myprotoai/demo/samples/circular/images/05-troubleshooting/53-solder-bridge-identification.png

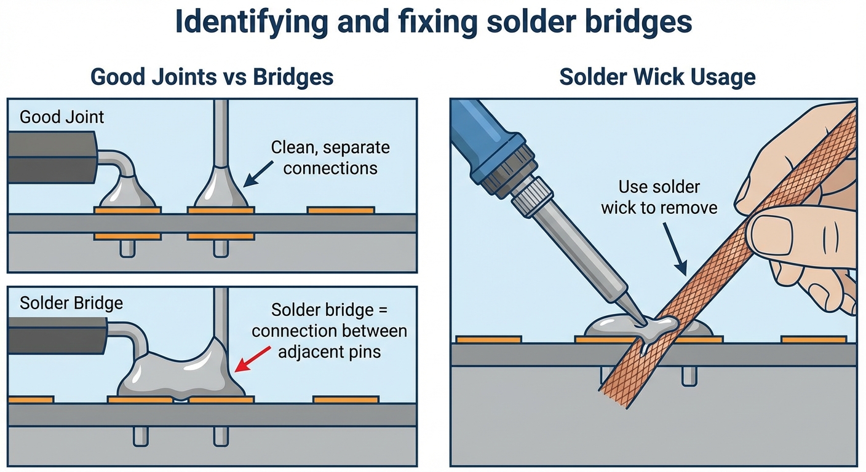
samples/circular/images/05-troubleshooting/53-solder-bridge-identification.png
