myprotoai/demo/samples/circular/images/05-troubleshooting/54-cold-solder-joints.png

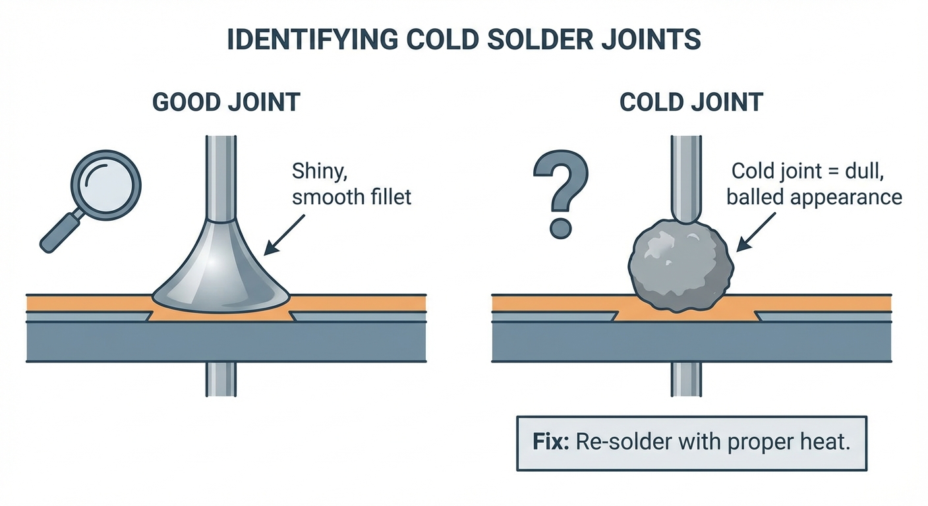
samples/circular/images/05-troubleshooting/54-cold-solder-joints.png
