myprotoai/demo/samples/teardrop/images/05-troubleshooting/53-solder-bridge-identification-teardrop.png

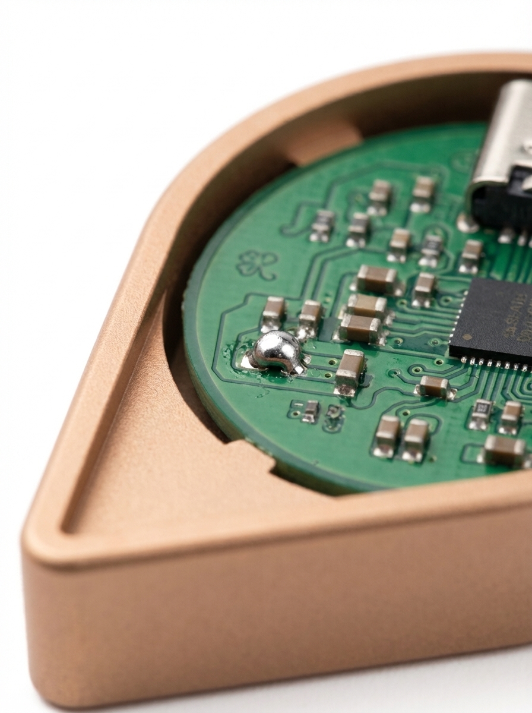
samples/teardrop/images/05-troubleshooting/53-solder-bridge-identification-teardrop.png
