myprotoai/demo/samples/teardrop/images/05-troubleshooting/54-cold-solder-joints-teardrop.png

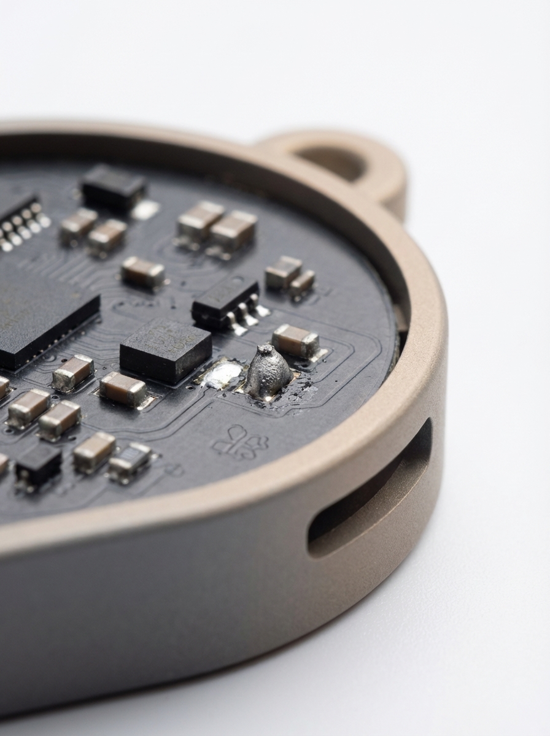
samples/teardrop/images/05-troubleshooting/54-cold-solder-joints-teardrop.png
